super-cow-powers/ThereMin/Other Pics/IMG_20230629_124354.jpg

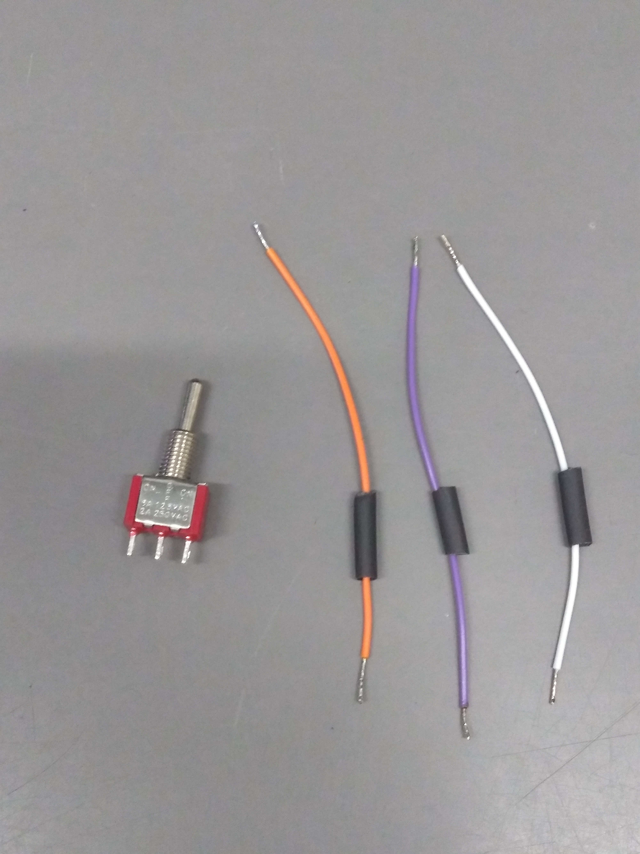
Other Pics/IMG_20230629_124354.jpg
