super-cow-powers/ThereMin/Software/Core/Inc/nucleo-l152_defs.h

#ifndef nL152DEFS_h
#define nL152DEFS_h

#define DAC_OUT_PIN 4
#define PITCH_PIN 1
#define VOLUME_PIN 6
#define CAL_PIN 7

#endif
