super-cow-powers/ThereMin/Software/Core/Inc/sys-setup.h

#ifndef SYSSETUP_h
#define SYSSETUP_h
#include <stdint.h>

#define FRQ_CNT_SAMPLES 256
#define VOL_CNT_SAMPLES 64
#define INITIAL_DAC_ARR 3000

extern volatile uint16_t volumeInputBuffer[VOL_CNT_SAMPLES];
extern volatile uint16_t pitchInputBuffer[FRQ_CNT_SAMPLES];

/** Init the platform */
void platform_init(void);

/** Enable SysTick */
void enable_tick (void);

/** Configure the GPIOs */
void configure_gpio(void);

/** Configure the system timers */
void configure_timers(void);

/** Start the audio output */
void start_output(void);

/** Configure the DAC */
void configure_dac(void);

/** Offset the DAC Timer from the initial time-base */
void offsetDacTimer(int32_t offset);

#endif
